inoa-io/satellite/electrics/ethernet-extension/ethernet-extension.kicad_pcb

## KiCad design electrics/ethernet-extension/ethernet-extension.kicad_pcb (2023-01-17)

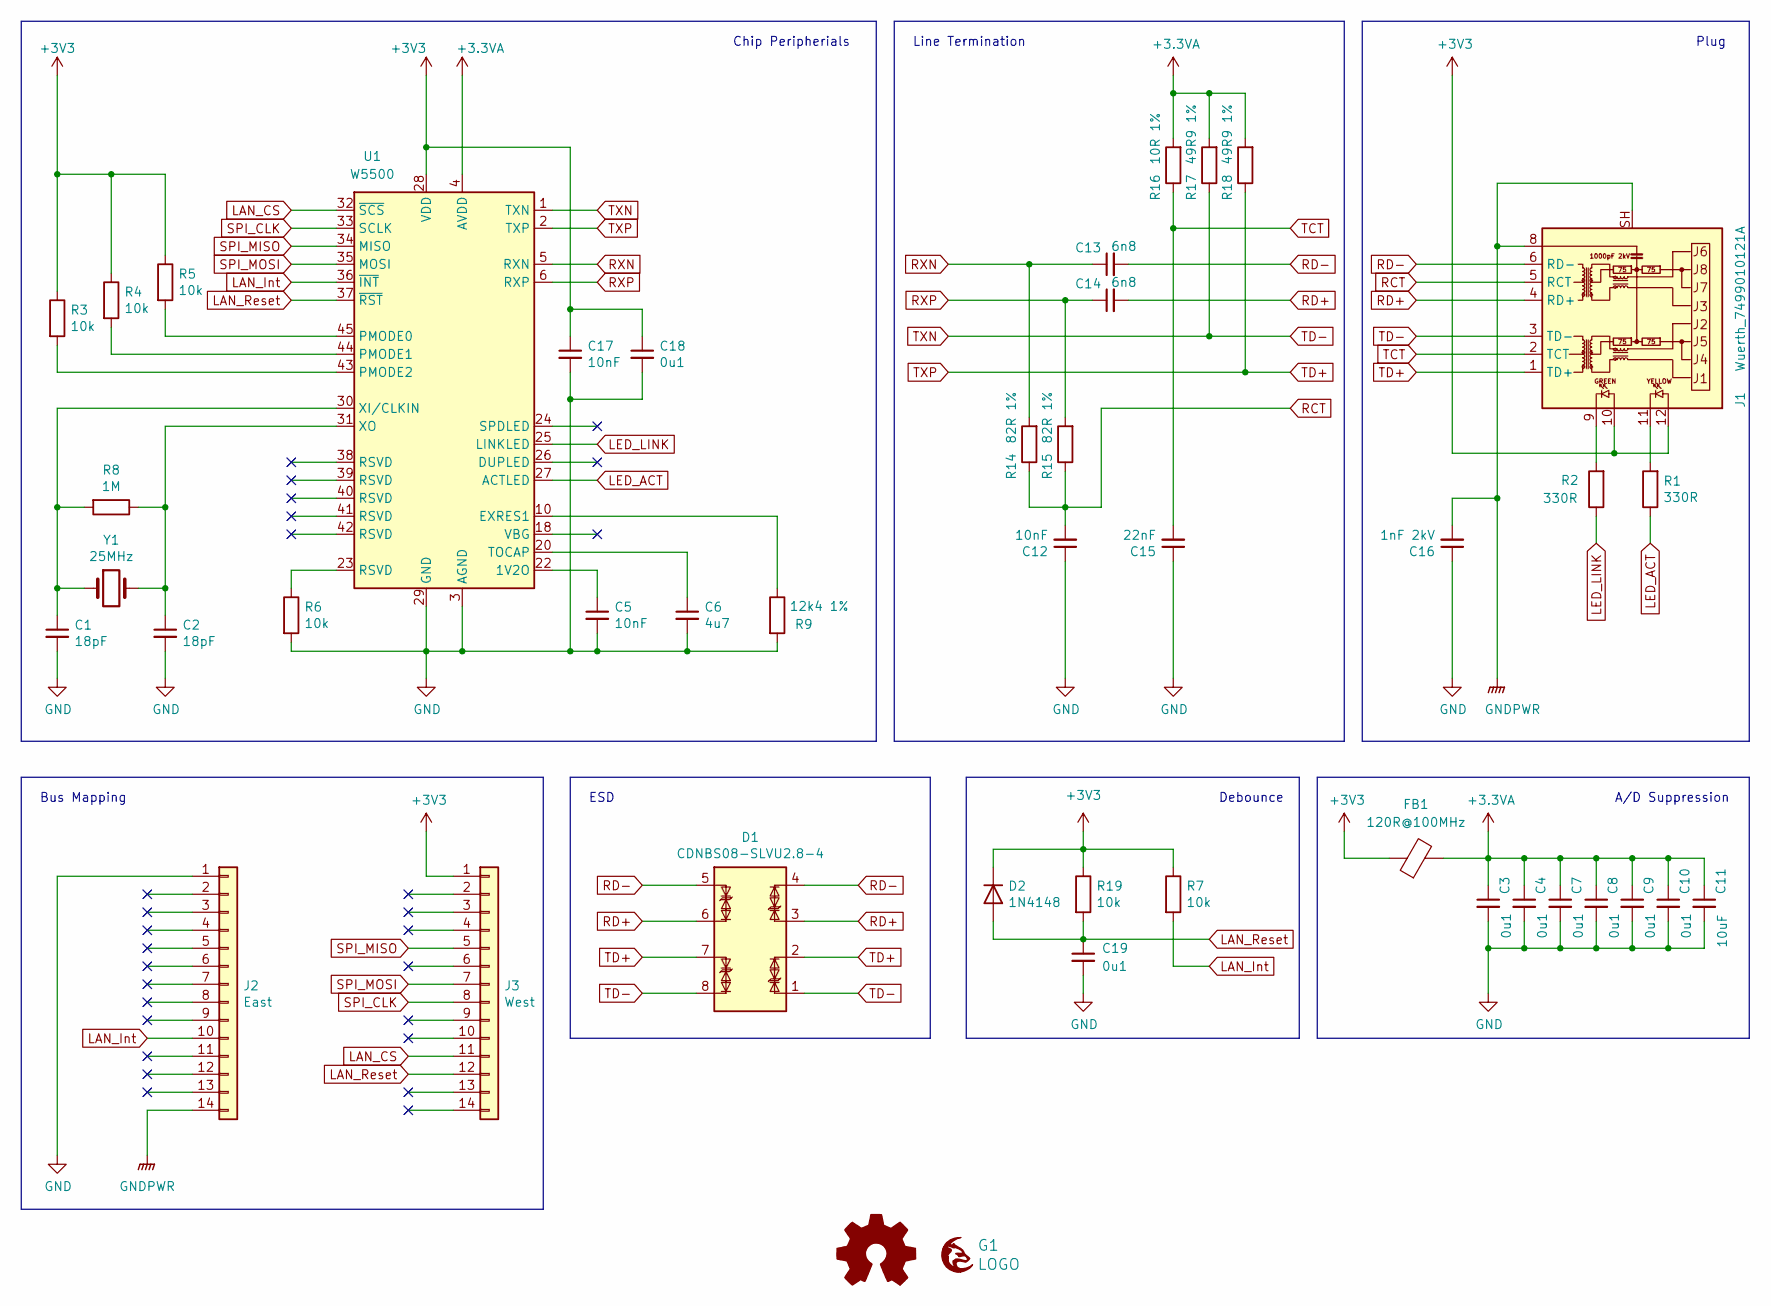
[picture p44: schematic ethernet-extension.kicad_sch, Inoa Satelite Ethernet Extension]

Parts:
C1, C2: 18pF; C_0603_1608Metric_Pad1.08x0.95mm_HandSolder
C3, C4, C7, C8, C9, C10, C18, C19: 0u1; C_0603_1608Metric_Pad1.08x0.95mm_HandSolder
C5, C12, C17: 10nF; C_0603_1608Metric_Pad1.08x0.95mm_HandSolder
C6: 4u7; C_0603_1608Metric_Pad1.08x0.95mm_HandSolder
C11: 10uF; C_0603_1608Metric_Pad1.08x0.95mm_HandSolder
C13, C14: 6n8; C_0603_1608Metric_Pad1.08x0.95mm_HandSolder
C15: 22nF; C_0603_1608Metric_Pad1.08x0.95mm_HandSolder
C16: 1nF 2kV; C_1812_4532Metric_Pad1.57x3.40mm_HandSolder
D1: CDNBS08-SLVU2.8-4; SOIC-8_3.9x4.9mm_P1.27mm
D2: 1N4148; D_SOD-323_HandSoldering
FB1: 120R@100MHz; L_0805_2012Metric
G1: LOGO; grayc-logo-negative
G2: Logo_Open_Hardware_Small; OSHW-Logo2_7.3x6mm_SilkScreen
J1: Wuerth_7499010121A; RJ45_Wuerth_7499010121A_Horizontal
J2: East; PinHeader_1x14_P2.54mm_Vertical
J3: West; PinHeader_1x14_P2.54mm_Vertical
R1, R2: 330R; R_0603_1608Metric_Pad0.98x0.95mm_HandSolder
R3, R4, R5, R6, R7, R19: 10k; R_0603_1608Metric_Pad0.98x0.95mm_HandSolder
R8: 1M; R_0603_1608Metric_Pad0.98x0.95mm_HandSolder
R9: 12k4 1%; R_0603_1608Metric_Pad0.98x0.95mm_HandSolder
R14, R15: 82R 1%; R_0603_1608Metric_Pad0.98x0.95mm_HandSolder
R16: 10R 1%; R_0603_1608Metric_Pad0.98x0.95mm_HandSolder
R17, R18: 49R9 1%; R_0603_1608Metric_Pad0.98x0.95mm_HandSolder
U1: W5500; LQFP-48_7x7mm_P0.5mm
Y1: 25MHz; Crystal_SMD_0603-2Pin_6.0x3.5mm_HandSoldering

Connections:
+3.3VA: C3.1, C4.1, C7.1, C8.1, C9.1, C10.1, C11.1, FB1.2, R16.2, R17.2, R18.2, U1.4 (AVDD), U1.8 (AVDD), U1.11 (AVDD), U1.15 (AVDD), U1.17 (AVDD), U1.21 (AVDD)
+3V3: C17.1, C18.1, D2.1 (K), FB1.1, J1.10, J1.12, J3.1, R3.1, R4.1, R5.1, R7.1, R19.1, U1.28 (VDD)
GND: C1.2, C2.2, C3.2, C4.2, C5.2, C6.2, C7.2, C8.2, C9.2, C10.2, C11.2, C12.1, C15.1, C16.1, C17.2, C18.2, C19.2, J2.1, R6.2, R9.2, U1.3 (AGND), U1.9 (AGND), U1.14 (AGND), U1.16 (AGND), U1.19 (AGND), U1.29 (GND), U1.48 (AGND)
GNDPWR: C16.2, J1.8, J1.SH, J2.14
LAN_CS: J3.11, U1.32 (~SCS)
LAN_Int: J2.10, R7.2, U1.36 (~INT)
LAN_Reset: C19.1, D2.2 (A), J3.12, R19.2, U1.37 (~RST)
LED_ACT: R1.1, U1.27 (ACTLED)
LED_LINK: R2.1, U1.25 (LINKLED)
unnamed: C1.1, R8.2, U1.30 (XI/CLKIN), Y1.1
unnamed: C2.1, R8.1, U1.31 (XO), Y1.2
unnamed: C5.1, U1.22 (1V2O)
unnamed: C6.1, U1.20 (TOCAP)
unnamed: J1.9, R2.2
unnamed: J1.11, R1.2
unnamed: R3.2, U1.43 (PMODE2)
unnamed: R4.2, U1.44 (PMODE1)
unnamed: R5.2, U1.45 (PMODE0)
unnamed: R6.1, U1.23 (RSVD)
unnamed: R9.1, U1.10 (EXRES1)
RCT: C12.2, J1.5 (RCT), R14.1, R15.1
RD+: C14.2, D1.3 (TVS1), D1.6 (TVS2), J1.4 (RD+)
RD-: C13.2, D1.4 (TVS2), D1.5 (TVS1), J1.6 (RD-)
RXN: C13.1, R14.2, U1.5 (RXN)
RXP: C14.1, R15.2, U1.6 (RXP)
SPI_CLK: J3.8, U1.33 (SCLK)
SPI_MISO: J3.5, U1.34 (MISO)
SPI_MOSI: J3.7, U1.35 (MOSI)
TCT: C15.2, J1.2 (TCT), R16.1
TD+: D1.2 (TVS2), D1.7 (TVS1), J1.1 (TD+), R18.1, U1.2 (TXP)
TD-: D1.1 (TVS1), D1.8 (TVS2), J1.3 (TD-), R17.1, U1.1 (TXN)

Notes on the sheet:
ESD
Debounce
A/D Suppression
Chip Peripherials
Plug
Line Termination
Bus Mapping

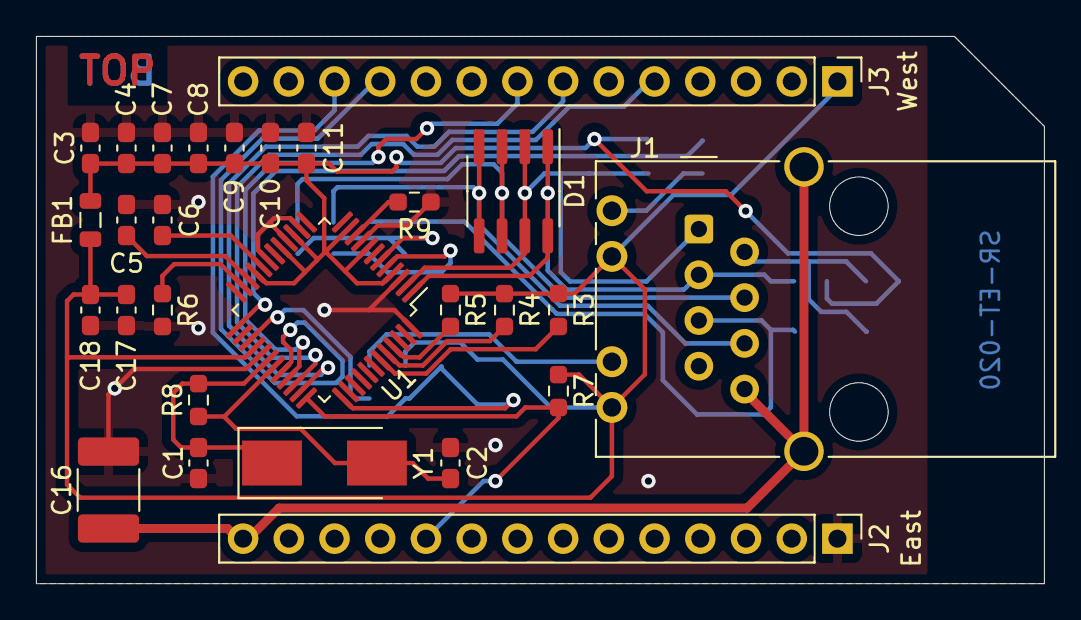
[picture p45: board ethernet-extension.kicad_pcb from above]

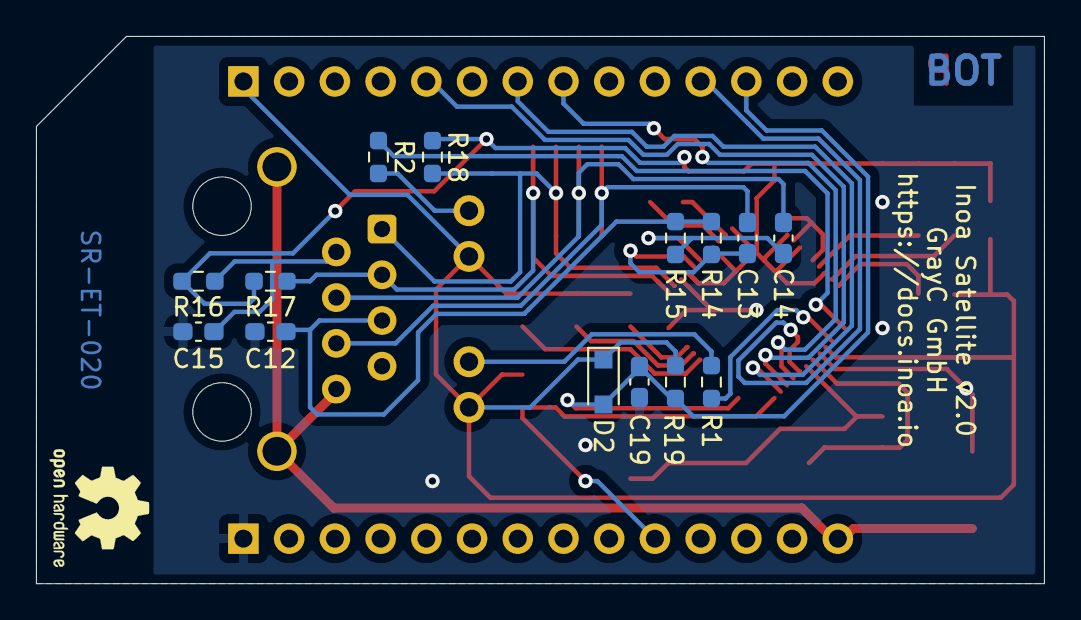
[picture p46: board ethernet-extension.kicad_pcb from below]

Board: 2 copper layers, 56.0 x 30.4 mm, 44 parts (16 on the bottom side), 31 nets.
