inoa-io/satellite/electrics/smart-meter-module/smart-meter-module.kicad_pcb

## KiCad design electrics/smart-meter-module/smart-meter-module.kicad_pcb (2023-01-19)

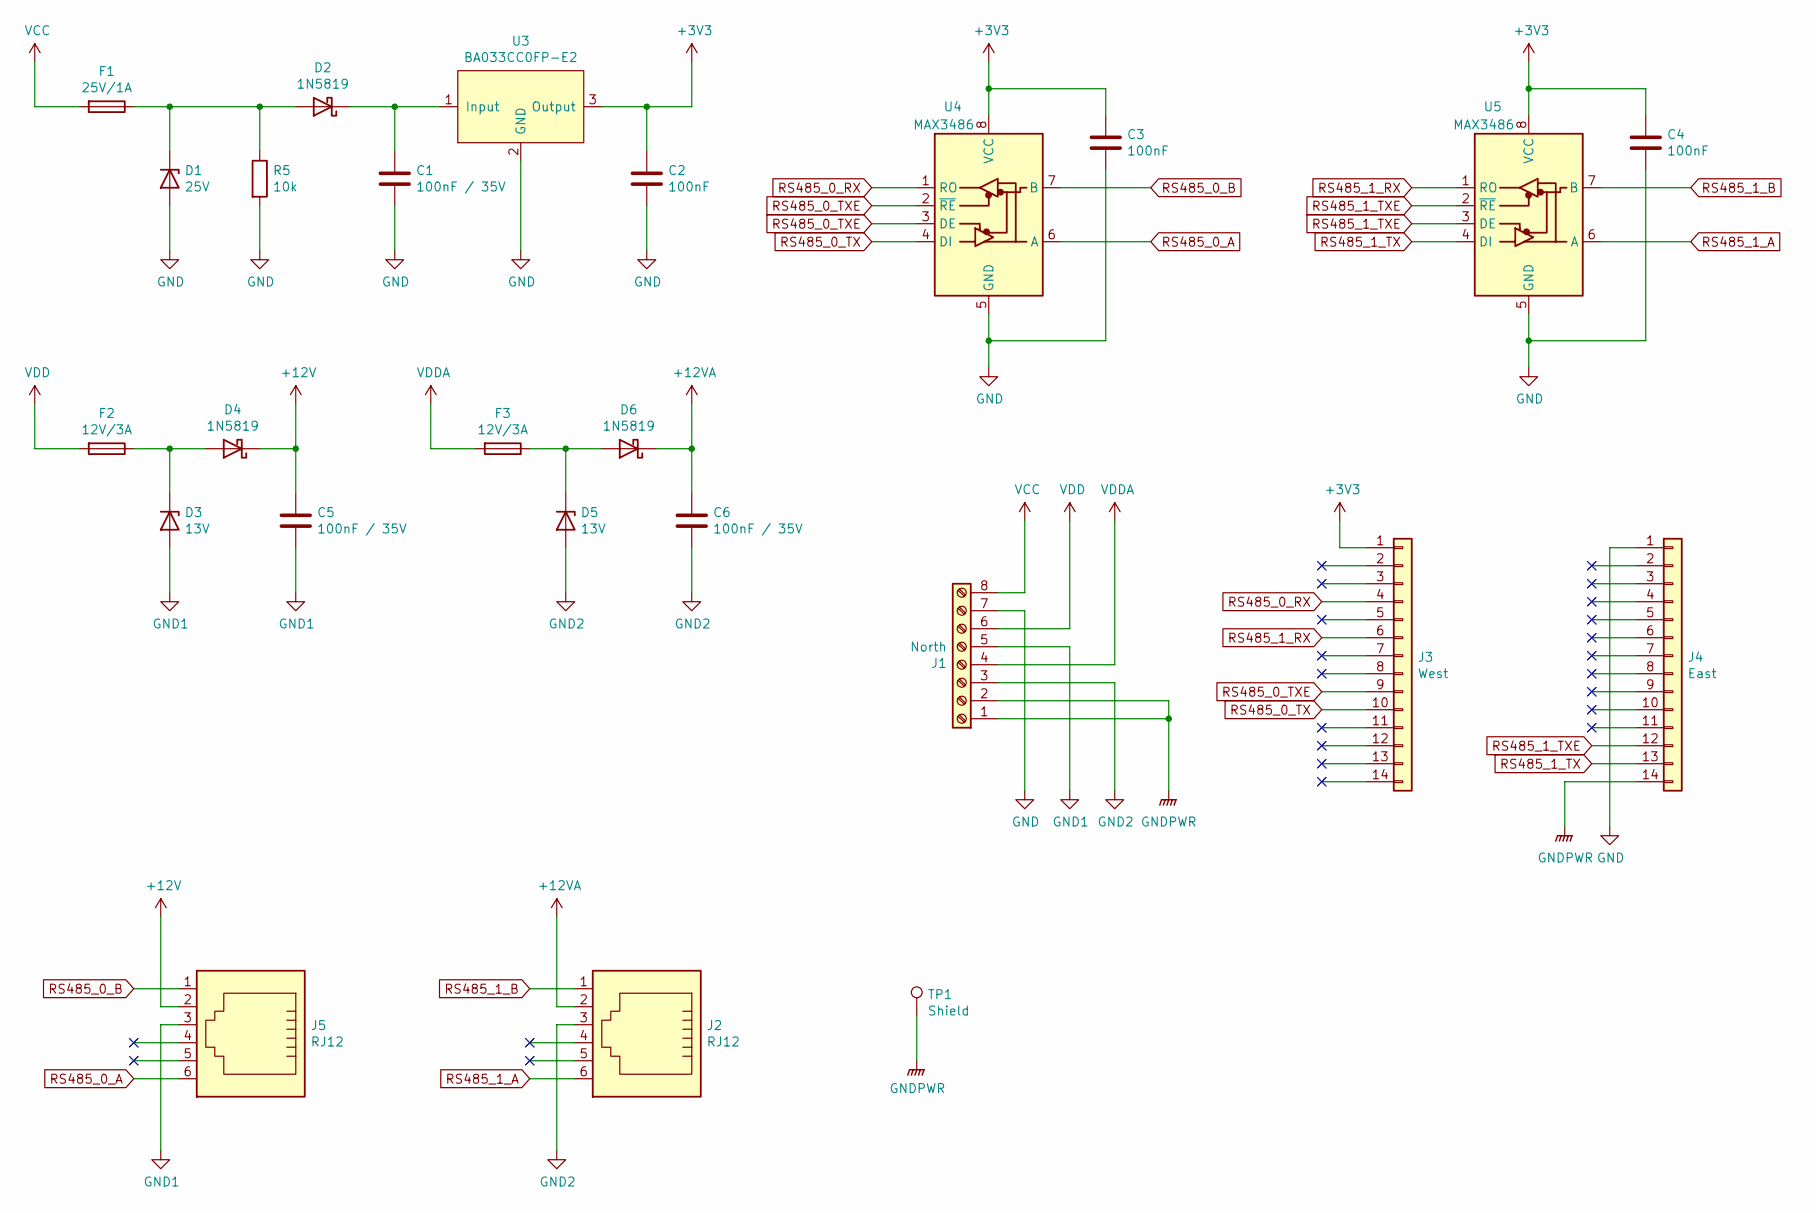
[picture p47: schematic smart-meter-module.kicad_sch, Electric Metering Module]

Parts:
C1, C5, C6: 100nF / 35V; C_1206_3216Metric_Pad1.33x1.80mm_HandSolder
C2, C3, C4: 100nF; C_1206_3216Metric_Pad1.33x1.80mm_HandSolder
D1: 25V; D_SOD-523
D2, D4, D6: 1N5819; D_SOD-323_HandSoldering
D3, D5: 13V; D_SOD-523
F1: 25V/1A; Fuse_1206_3216Metric_Pad1.42x1.75mm_HandSolder
F2, F3: 12V/3A; Fuse_1206_3216Metric_Pad1.42x1.75mm_HandSolder
J1: North; PHOENIX_1727078
J2, J5: RJ12; Molex-95501-6669-MFG
J3: West; PinHeader_1x14_P2.54mm_Vertical
J4: East; PinHeader_1x14_P2.54mm_Vertical
R5: 10k; R_1206_3216Metric_Pad1.30x1.75mm_HandSolder
TP1: Shield; TestPoint_Pad_D4.0mm
U3: BA033CC0FP-E2; TO-252-3_TabPin2
U4, U5: MAX3486; SOIC-8_3.9x4.9mm_P1.27mm

Connections:
+3V3: C2.1, C3.1, C4.1, J3.1, U3.3 (Output), U4.8 (VCC), U5.8 (VCC)
+12V: C5.1, D4.1 (K), J5.2
+12VA: C6.1, D6.1 (K), J2.2
GND: C1.2, C2.2, C3.2, C4.2, D1.2 (A), J1.7, J4.1, R5.2, U3.2 (GND), U4.5 (GND), U5.5 (GND)
GND1: C5.2, D3.2 (A), J1.5, J5.3
GND2: C6.2, D5.2 (A), J1.3, J2.3
GNDPWR: J1.1, J1.2, J4.14, TP1.1
unnamed: C1.1, D2.1 (K), U3.1 (Input)
unnamed: D1.1 (K), D2.2 (A), F1.1, R5.1
unnamed: D3.1 (K), D4.2 (A), F2.1
unnamed: D5.1 (K), D6.2 (A), F3.1
RS485_0_A: J5.6, U4.6 (A)
RS485_0_B: J5.1, U4.7 (B)
RS485_0_RX: J3.4, U4.1 (RO)
RS485_0_TX: J3.10, U4.4 (DI)
RS485_0_TXE: J3.9, U4.2 (~RE), U4.3 (DE)
RS485_1_A: J2.6, U5.6 (A)
RS485_1_B: J2.1, U5.7 (B)
RS485_1_RX: J3.6, U5.1 (RO)
RS485_1_TX: J4.13, U5.4 (DI)
RS485_1_TXE: J4.12, U5.2 (~RE), U5.3 (DE)
VCC: F1.2, J1.8
VDD: F2.2, J1.6
VDDA: F3.2, J1.4

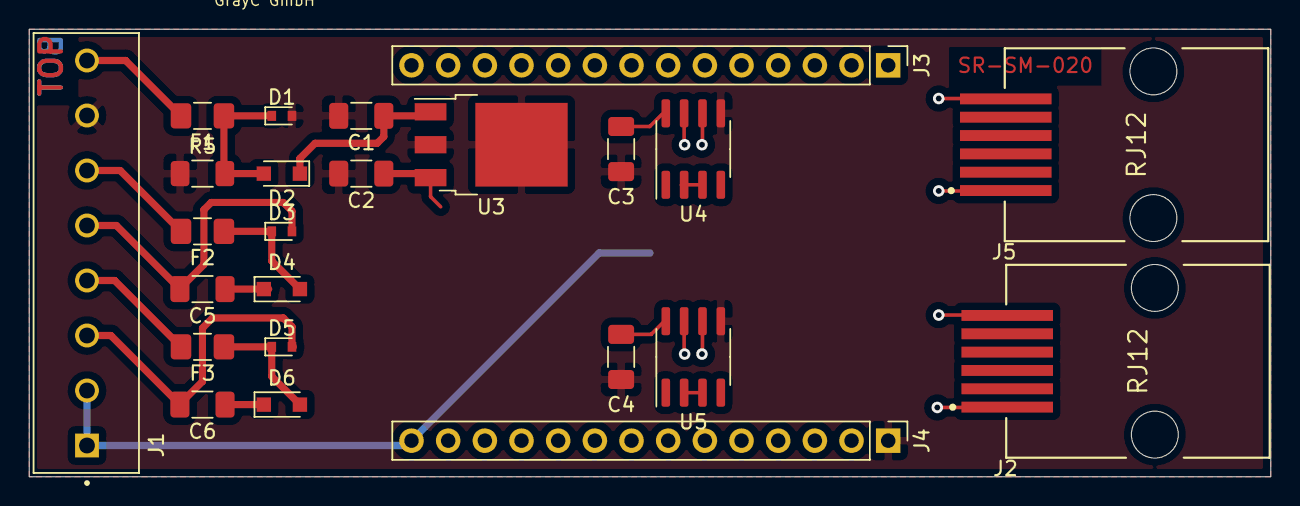
[picture p48: board smart-meter-module.kicad_pcb from above]

Board: 2 copper layers, 86.0 x 31.0 mm, 25 parts (1 on the bottom side), 24 nets.
