inoa-io/satellite/electrics/lora-module/lora-module.kicad_pcb

## KiCad design electrics/lora-module/lora-module.kicad_pcb (2023-01-19)

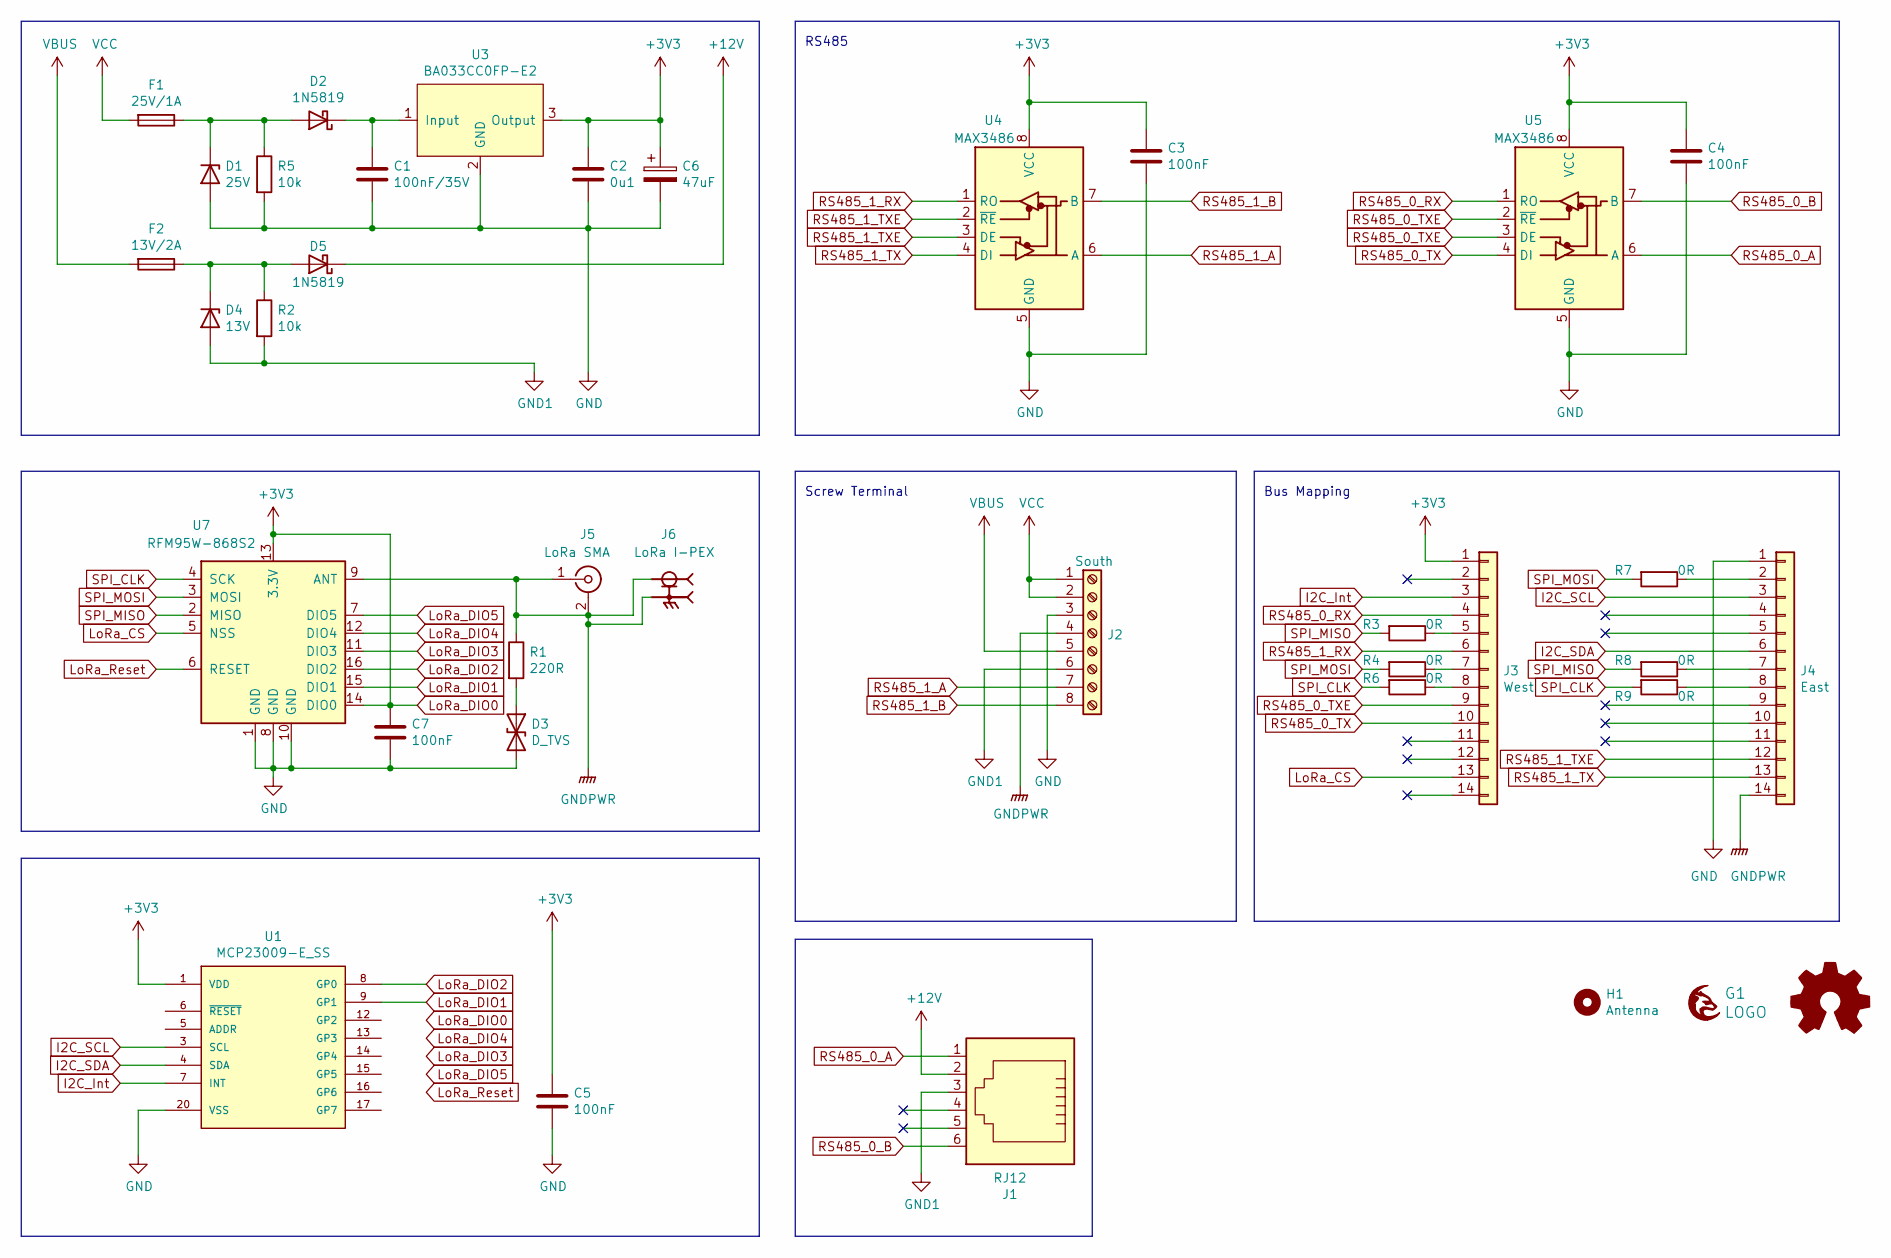
[picture p49: schematic lora-module.kicad_sch, LoRa LMN Metering Module]

Parts:
C1: 100nF/35V; C_1206_3216Metric_Pad1.33x1.80mm_HandSolder
C2: 0u1; C_1206_3216Metric_Pad1.33x1.80mm_HandSolder
C3, C4, C5, C7: 100nF; C_1206_3216Metric_Pad1.33x1.80mm_HandSolder
C6: 47uF; CP_Elec_5x5.3
D1: 25V; D_SOD-523
D2, D5: 1N5819; D_SOD-323_HandSoldering
D3: D_TVS; D_0603_1608Metric_Pad1.05x0.95mm_HandSolder
D4: 13V; D_SOD-523
F1: 25V/1A; Fuse_1206_3216Metric_Pad1.42x1.75mm_HandSolder
F2: 13V/2A; Fuse_1206_3216Metric_Pad1.42x1.75mm_HandSolder
G1: LOGO; grayc-logo-negative
G2: Logo_Open_Hardware_Small; OSHW-Logo2_7.3x6mm_SilkScreen
H1: Antenna; MountingHole_3.7mm
J1: RJ12; CUI_CRJ030-G-TH
J2: South; PHOENIX_1727078
J3: West; PinHeader_1x14_P2.54mm_Vertical
J4: East; PinHeader_1x14_P2.54mm_Vertical
J5: LoRa SMA; LINX_CONSMA002
J6: LoRa I-PEX; SAMTEC_RSP-122811-01; PARTREV H
R1: 220R; R_1206_3216Metric_Pad1.30x1.75mm_HandSolder
R2, R5: 10k; R_1206_3216Metric_Pad1.30x1.75mm_HandSolder
R3, R4, R6, R7, R8, R9: 0R; R_1206_3216Metric_Pad1.30x1.75mm_HandSolder
U1: MCP23009-E_SS; SOP65P780X200-20N; PARTREV C
U3: BA033CC0FP-E2; TO-252-3_TabPin2
U4, U5: MAX3486; SOIC-8_3.9x4.9mm_P1.27mm
U7: RFM95W-868S2; XCVR_RFM69HW-868S2

Connections:
+12V: D5.1 (K), J1.2
GND: C1.2, C2.2, C3.2, C4.2, C5.2, C6.2, C7.2, D1.2 (A), D3.2 (A2), J2.3, J4.1, R5.2, U1.20 (VSS), U3.2 (GND), U4.5 (GND), U5.5 (GND), U7.1 (GND), U7.8 (GND), U7.10 (GND)
GND1: D4.2 (A), J1.3, J2.6, R2.2
I2C_Int: J3.3, U1.7 (INT)
I2C_SCL: J4.3, U1.3 (SCL)
I2C_SDA: J4.6, U1.4 (SDA)
LoRa_CS: J3.13, U7.5 (NSS)
LoRa_DIO1: U1.9 (GP1), U7.15 (DIO1)
LoRa_DIO2: U1.8 (GP0), U7.16 (DIO2)
LoRa_DIO3: U7.11 (DIO3)
LoRa_DIO4: U7.12 (DIO4)
LoRa_DIO5: U7.7 (DIO5)
LoRa_Reset: U7.6 (RESET)
unnamed: C1.1, D2.1 (K), U3.1 (Input)
unnamed: D1.1 (K), D2.2 (A), F1.1, R5.1
unnamed: D3.1 (A1), R1.2
unnamed: D4.1 (K), D5.2 (A), F2.1, R2.1
unnamed: J3.5, R3.1
unnamed: J3.7, R4.1
unnamed: J3.8, R6.1
unnamed: J4.2, R7.1
unnamed: J4.7, R8.1
unnamed: J4.8, R9.1
RS485_0_A: J1.1, U5.6 (A)
RS485_0_B: J1.6, U5.7 (B)
RS485_0_RX: J3.4, U5.1 (RO)
RS485_0_TX: J3.10, U5.4 (DI)
RS485_0_TXE: J3.9, U5.2 (~RE), U5.3 (DE)
RS485_1_A: J2.7, U4.6 (A)
RS485_1_B: J2.8, U4.7 (B)
RS485_1_RX: J3.6, U4.1 (RO)
RS485_1_TX: J4.13, U4.4 (DI)
RS485_1_TXE: J4.12, U4.2 (~RE), U4.3 (DE)
SPI_CLK: R6.2, R9.2, U7.4 (SCK)
SPI_MISO: R3.2, R8.2, U7.2 (MISO)
SPI_MOSI: R4.2, R7.2, U7.3 (MOSI)
VBUS: F2.2, J2.5
VCC: F1.2, J2.1, J2.2

Notes on the sheet:
RS485
Bus Mapping
Screw Terminal

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
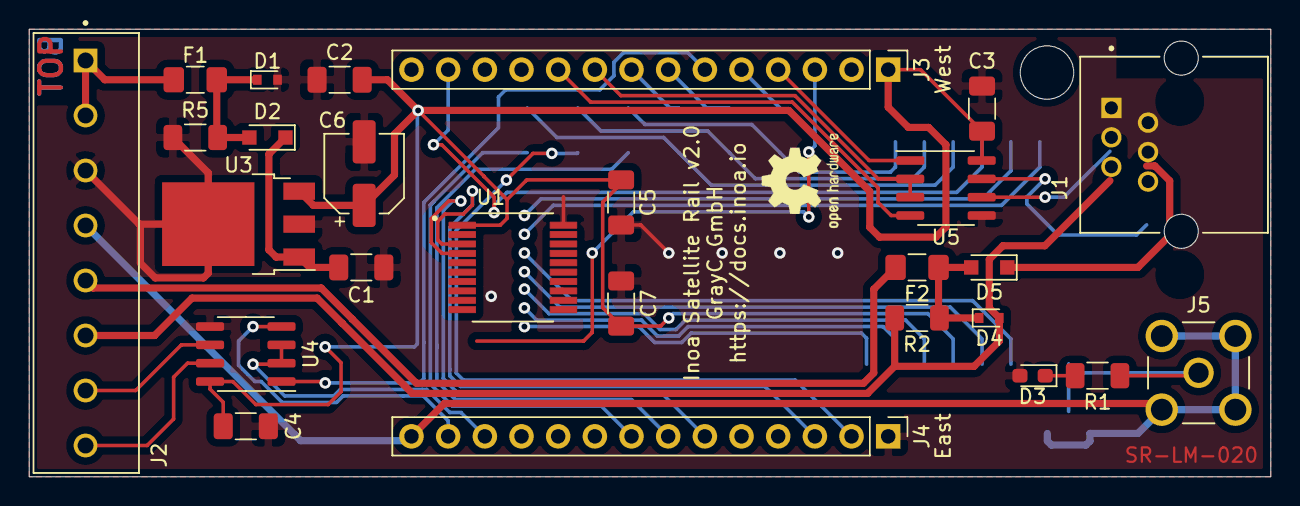
[picture p50: board lora-module.kicad_pcb from above]

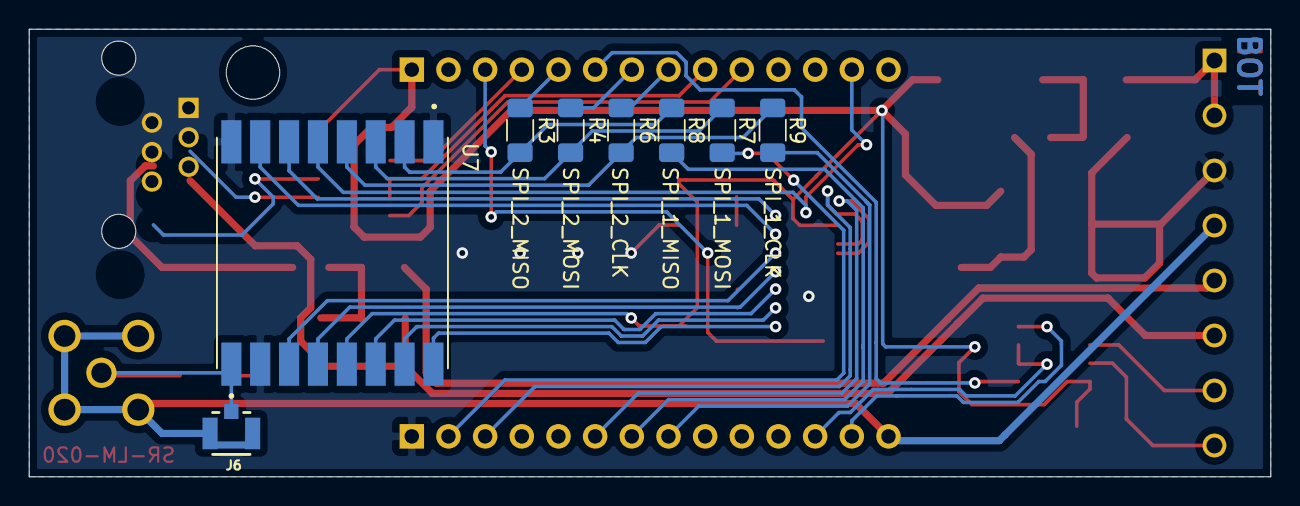
[picture p51: board lora-module.kicad_pcb from below]

Board: 2 copper layers, 86.0 x 31.0 mm, 37 parts (8 on the bottom side), 37 nets.
